Nangman-Dolphins/GreenEye_SensorDevice/Hardware/Standard Version/Schematic/Schematic_GreenEye_SensorModule.pdf

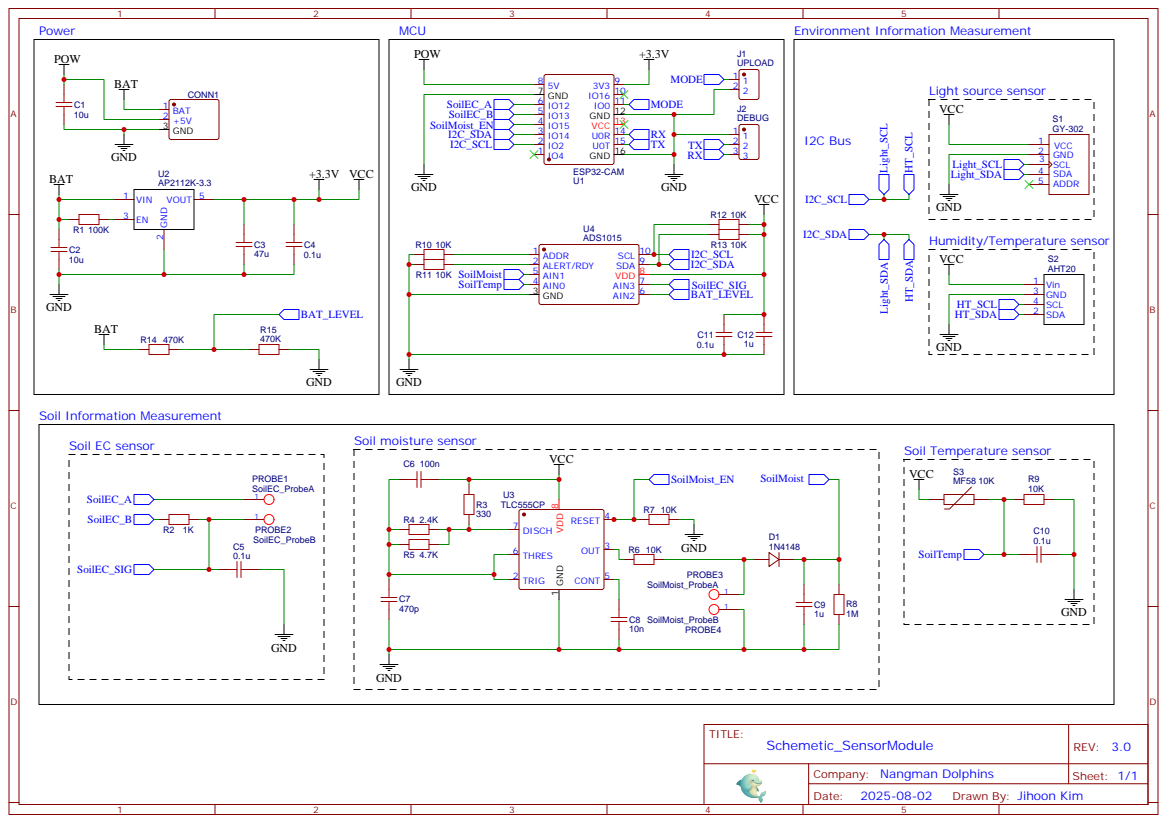
[picture p43: page 1]

Drawn By: Jihoon Kim
